terriblefire/tf0060dca/measured/raw_curve_second_measure.csv

0 | 3.879E-02
1 | 4.814E-02
2 | 4.548E-02
3 | 4.712E-02
4 | 3.746E-02
5 | 4.777E-02
6 | 4.367E-02
7 | 4.940E-02
8 | 4.769E-02
9 | 4.725E-02
10 | 4.829E-02
11 | 4.766E-02
12 | 5.000E-02
13 | 4.697E-02
14 | 4.407E-02
15 | 4.691E-02
16 | 3.960E-02
17 | 4.721E-02
18 | 4.436E-02
19 | 2.935E-02
20 | 4.569E-02
21 | 3.824E-02
22 | 4.596E-02
23 | 2.173E-02
24 | 4.737E-02
25 | 4.589E-02
26 | 3.364E-02
27 | 5.176E-02
28 | 4.321E-02
29 | 4.673E-02
30 | 4.359E-02
31 | 4.727E-02
32 | 4.730E-02
33 | 4.228E-02
34 | 5.061E-02
35 | 4.380E-02
36 | 4.621E-02
37 | 4.445E-02
38 | 5.042E-02
39 | 3.846E-02
40 | 4.711E-02
41 | 4.800E-02
42 | 4.568E-02
43 | 4.769E-02
44 | 4.675E-02
45 | 4.620E-02
46 | 4.627E-02
47 | 4.630E-02
48 | 4.316E-02
49 | 4.720E-02
50 | 4.120E-02
51 | 4.403E-02
52 | 4.741E-02
53 | 3.936E-02
54 | 4.137E-02
55 | 4.700E-02
56 | 3.302E-02
57 | 4.000E-02
58 | 4.460E-02
59 | 4.626E-02
60 | 4.956E-02
61 | 4.145E-02
62 | 4.582E-02
63 | 4.612E-02
64 | 2.395E-02
65 | 4.552E-02
66 | 4.825E-02
67 | 2.278E-02
68 | 4.247E-02
69 | 2.898E-02
70 | 4.631E-02
71 | 3.664E-02
72 | 4.887E-02
73 | 4.615E-02
74 | 5.056E-02
75 | 4.279E-02
76 | 4.473E-02
77 | 4.749E-02
78 | 4.215E-02
79 | 3.435E-02
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
