terriblefire/tf0060dca/measured/repro_measure.csv

0 | 2.67E-02
1 | 2.67E-02
2 | 2.69E-02
3 | 2.68E-02
4 | 2.68E-02
5 | 2.70E-02
6 | 2.68E-02
7 | 2.70E-02
8 | 2.99E-02
9 | 2.97E-02
10 | 2.98E-02
11 | 2.99E-02
12 | 2.98E-02
13 | 2.98E-02
14 | 2.99E-02
15 | 3.00E-02
16 | 3.19E-02
17 | 3.18E-02
18 | 3.17E-02
19 | 3.18E-02
20 | 3.20E-02
21 | 3.18E-02
22 | 3.19E-02
23 | 3.19E-02
24 | 3.70E-02
25 | 3.70E-02
26 | 3.71E-02
27 | 3.70E-02
28 | 3.69E-02
29 | 3.71E-02
30 | 3.71E-02
31 | 3.70E-02
32 | 4.24E-02
33 | 4.25E-02
34 | 4.26E-02
35 | 4.27E-02
36 | 4.23E-02
37 | 4.24E-02
38 | 4.24E-02
39 | 4.23E-02
40 | 4.63E-02
41 | 4.62E-02
42 | 4.61E-02
43 | 4.63E-02
44 | 4.62E-02
45 | 4.63E-02
46 | 4.62E-02
47 | 4.61E-02
48 | 5.46E-02
49 | 5.46E-02
50 | 5.46E-02
51 | 5.47E-02
52 | 5.47E-02
53 | 5.45E-02
54 | 5.48E-02
55 | 5.48E-02
56 | 6.43E-02
57 | 6.44E-02
58 | 6.44E-02
59 | 6.42E-02
60 | 6.43E-02
61 | 6.42E-02
62 | 6.43E-02
63 | 6.43E-02
64 | 7.13E-02
65 | 7.16E-02
66 | 7.16E-02
67 | 7.15E-02
68 | 7.14E-02
69 | 7.17E-02
70 | 7.15E-02
71 | 7.16E-02
72 | 8.54E-02
73 | 8.55E-02
74 | 8.57E-02
75 | 8.55E-02
76 | 8.55E-02
77 | 8.56E-02
78 | 8.56E-02
79 | 8.56E-02
80 | 1.023E-01
81 | 1.019E-01
82 | 1.021E-01
83 | 1.021E-01
84 | 1.022E-01
85 | 1.021E-01
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
