terriblefire/tf0060dca/measured/response_half_volt_pp.csv

0 | 8.75E-03
1 | 9.60E-03
2 | 2.496E-02
3 | 2.111E-02
4 | 6.28E-03
5 | 5.13E-03
6 | 2.414E-02
7 | 2.396E-02
8 | 1.173E-02
9 | 9.23E-03
10 | 2.583E-02
11 | 7.49E-03
12 | 2.796E-02
13 | 2.455E-02
14 | 9.48E-03
15 | 8.01E-03
16 | 2.732E-02
17 | 1.039E-02
18 | 1.406E-02
19 | 1.210E-02
20 | 2.524E-02
21 | 1.205E-02
22 | 2.343E-02
23 | 2.397E-02
24 | 9.43E-03
25 | 1.468E-02
26 | 2.497E-02
27 | 2.588E-02
28 | 1.091E-02
29 | 7.71E-03
30 | 2.731E-02
31 | 7.91E-03
32 | 1.028E-02
33 | 2.365E-02
34 | 1.868E-02
35 | 1.347E-02
36 | 1.328E-02
37 | 5.12E-03
38 | 2.645E-02
39 | 6.57E-03
40 | 1.030E-02
41 | 9.48E-03
42 | 1.410E-02
43 | 9.94E-03
44 | 1.255E-02
45 | 1.749E-02
46 | 2.411E-02
47 | 8.86E-03
48 | 1.555E-02
49 | 2.478E-02
50 | 2.240E-02
51 | 1.648E-02
52 | 7.50E-03
53 | 1.210E-02
54 | 2.231E-02
55 | 1.279E-02
56 | 1.063E-02
57 | 9.82E-03
58 | 2.383E-02
59 | 1.556E-02
60 | 1.068E-02
61 | 2.371E-02
62 | 1.815E-02
63 | 2.501E-02
64 | 1.352E-02
65 | 1.161E-02
66 | 1.874E-02
67 | 2.123E-02
68 | 1.328E-02
69 | 2.508E-02
70 | 8.87E-03
71 | 2.596E-02
72 | 6.05E-03
73 | 1.152E-02
74 | 7.05E-03
75 | 2.261E-02
76 | 1.148E-02
77 | 2.440E-02
78 | 1.583E-02
79 | 2.560E-02
80 | 6.66E-03
81 | 1.456E-02
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
