terriblefire/tf0060dca/measured/response_one_point_two.csv

0 | 5.837E-02
1 | 6.016E-02
2 | 5.965E-02
3 | 5.769E-02
4 | 4.828E-02
5 | 5.565E-02
6 | 5.985E-02
7 | 6.062E-02
8 | 5.983E-02
9 | 2.890E-02
10 | 5.972E-02
11 | 5.479E-02
12 | 5.836E-02
13 | 6.029E-02
14 | 6.020E-02
15 | 6.380E-02
16 | 5.410E-02
17 | 6.364E-02
18 | 6.469E-02
19 | 5.781E-02
20 | 5.966E-02
21 | 5.921E-02
22 | 5.564E-02
23 | 5.931E-02
24 | 6.144E-02
25 | 5.686E-02
26 | 5.784E-02
27 | 5.902E-02
28 | 5.924E-02
29 | 4.763E-02
30 | 4.695E-02
31 | 5.226E-02
32 | 5.985E-02
33 | 5.274E-02
34 | 5.753E-02
35 | 5.673E-02
36 | 5.843E-02
37 | 5.471E-02
38 | 5.790E-02
39 | 5.912E-02
40 | 5.324E-02
41 | 5.842E-02
42 | 6.282E-02
43 | 4.750E-02
44 | 5.869E-02
45 | 5.663E-02
46 | 5.541E-02
47 | 6.029E-02
48 | 5.144E-02
49 | 5.040E-02
50 | 5.181E-02
51 | 5.913E-02
52 | 5.960E-02
53 | 5.851E-02
54 | 5.812E-02
55 | 6.163E-02
56 | 5.640E-02
57 | 5.722E-02
58 | 5.524E-02
59 | 5.921E-02
60 | 5.779E-02
61 | 5.498E-02
62 | 5.925E-02
63 | 5.790E-02
64 | 5.707E-02
65 | 5.978E-02
66 | 5.954E-02
67 | 5.869E-02
68 | 3.019E-02
69 | 6.090E-02
70 | 5.131E-02
71 | 6.293E-02
72 | 5.872E-02
73 | 5.993E-02
74 | 5.311E-02
75 | 5.979E-02
76 | 5.705E-02
77 | 5.971E-02
78 | 6.041E-02
79 | 6.305E-02
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
